liamsalter11/senior-design-14/TX_code/TX_sketch/correctionTX_rf/LiFiTXController.hpp

#ifndef LIFITXCONTROLLER
#define LIFITXCONTROLLER

#include "Bitset.hpp"

namespace LiFiTXController
{
	void TXOneChannel(const LiFiData::Bitset&);
	void TXThreeChannel(const LiFiData::Bitset&);
	
	void setAllLEDs(bool);
}

#endif
