liamsalter11/senior-design-14/RX_code/RX_sketch_rf/LiFiRXInterrupts.cpp

#include "LiFiRXInterrupts.hpp"
#include "LiFiRXConsts.hpp"

#include <Arduino.h>

volatile bool hitFrame = false;

void frameIntHandler()
{
	hitFrame = true;
}

void LiFiRXInterrupts::waitForFrameInterrupt()
{
  attachInterrupt(digitalPinToInterrupt(interruptPin), frameIntHandler, RISING);
  hitFrame = false;
	while (!hitFrame);
  detachInterrupt(digitalPinToInterrupt(interruptPin));
}
