liamsalter11/senior-design-14/RX_code/RX_sketch_rf/LiFiRXConsts.hpp

#ifndef LIFIRXCONSTS
#define LIFIRXCONSTS

const int BLUE = 7;
const int GREEN = 9;
const int RED = 10;
const int CLK = 9;
const int interruptPin = 13;
const int interruptControllerPin = 12;
const int maxSize = 200;
const int maxFrames = 100;
const int transRate = 1000; //us
const int frameSize = 10;

const bool USE_CORRECTION = true;

#endif
