liamsalter11/senior-design-14/RX_code/RX_sketch_rf/LiFiRXLink.hpp

#ifndef LIFIRXLINK
#define LIFIRXLINK

#include "Bitset.hpp"

namespace LiFiRXLink
{
	LiFiData::Bitset getFrameOneChannel();

	LiFiData::Bitset getFrameTwoChannel();

	LiFiData::Bitset getFrameThreeChannel();
}

#endif
