liamsalter11/senior-design-14/RX_code/RX_sketch_rf/LiFiRXSampling.hpp

#ifndef LIFIRXSAMPLER
#define LIFIRXSAMPLER

#include "Bitset.hpp"
#include "Pinset.hpp"

namespace LiFiRXSampling
{
	//Returns a frame of the given length*number of pins
	LiFiData::Bitset readFrame(const int, const LiFiData::Pinset&);
}

#endif
