liamsalter11/senior-design-14/TX_code/TX_sketch/correctionTX_rf/LiFiTXSerial.hpp

#ifndef LIFITXSERIAL
#define LIFITXSERIAL

#include "Bitset.hpp"

namespace LiFiTXSerial
{
	void initialize();
	void reset();
	void writeStartUpMessage(void);
	void writeBitset(const LiFiData::Bitset&);
	
	String getInputMessage();
}

#endif
