liamsalter11/senior-design-14/RX_code/RX_sketch/LiFiCorrection.hpp

#ifndef LIFICORRECTION
#define LIFICORRECTION

#include "Bitset.hpp"

namespace LiFiCorrection
{	
	LiFiData::Bitset convolve(const LiFiData::Bitset&);
	LiFiData::Bitset decodeErrors(const LiFiData::Bitset&);
};

#endif
