liamsalter11/senior-design-14/TX_code/TX_interface/TransmitInterface.py

import serial
import time
import os.path
from os import path

com = input("Enter COM port number:\n")

mcu = serial.Serial("COM" + com, 19200, timeout = 0.1)

while(True):
    choice = input("\nPlease select:\n\t(1) Text Input\n\t(2) File Input\n\t(3) Exit\n")
    if choice == '2':
        path = input("\nEnter file path of text document to transmit:\n")
        if os.path.exists(path):
            f = open(path, 'r').readlines()
        else:
            print("Invalid File Path")
            continue

        for line in f:
            try:
                mcu.write(line.encode())
            except:
                mcu.close()
                print("ERROR! Device disconnected.\n")
                quit()
            time.sleep(0.19)
    elif choice == '1':
        textInput = input("Please enter text:\n") + '\n'
        mcu.write(textInput.encode())
        #time.sleep(0.1)
    elif choice == '4':
        f = open("Bee_stripped.txt", 'r').readlines()
        for line in f:
            try:
                mcu.write(line.encode())
            except:
                mcu.close()
                print("ERROR! Device disconnected.\n")
                quit()
            time.sleep(0.19)
    else:
        break

    print('\n')
